Jm-47/ClockF30/images/IMG_1591.jpeg

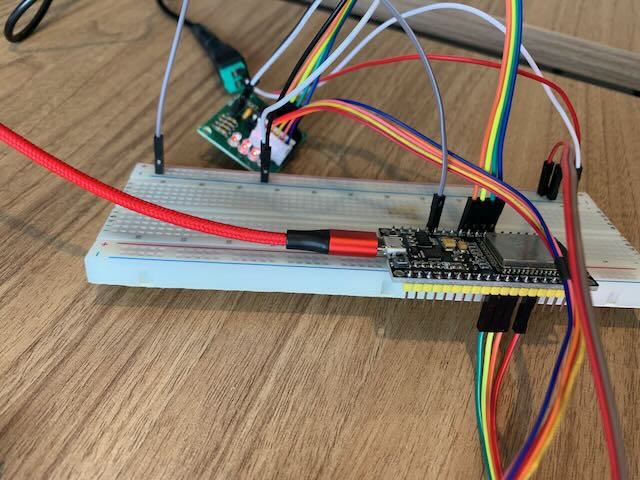
images/IMG_1591.jpeg
